samukallio/retro-z80/hardware/kicad/video.kicad_sch

## KiCad design hardware/kicad/video.kicad_sch (2024-03-21, an earlier design)

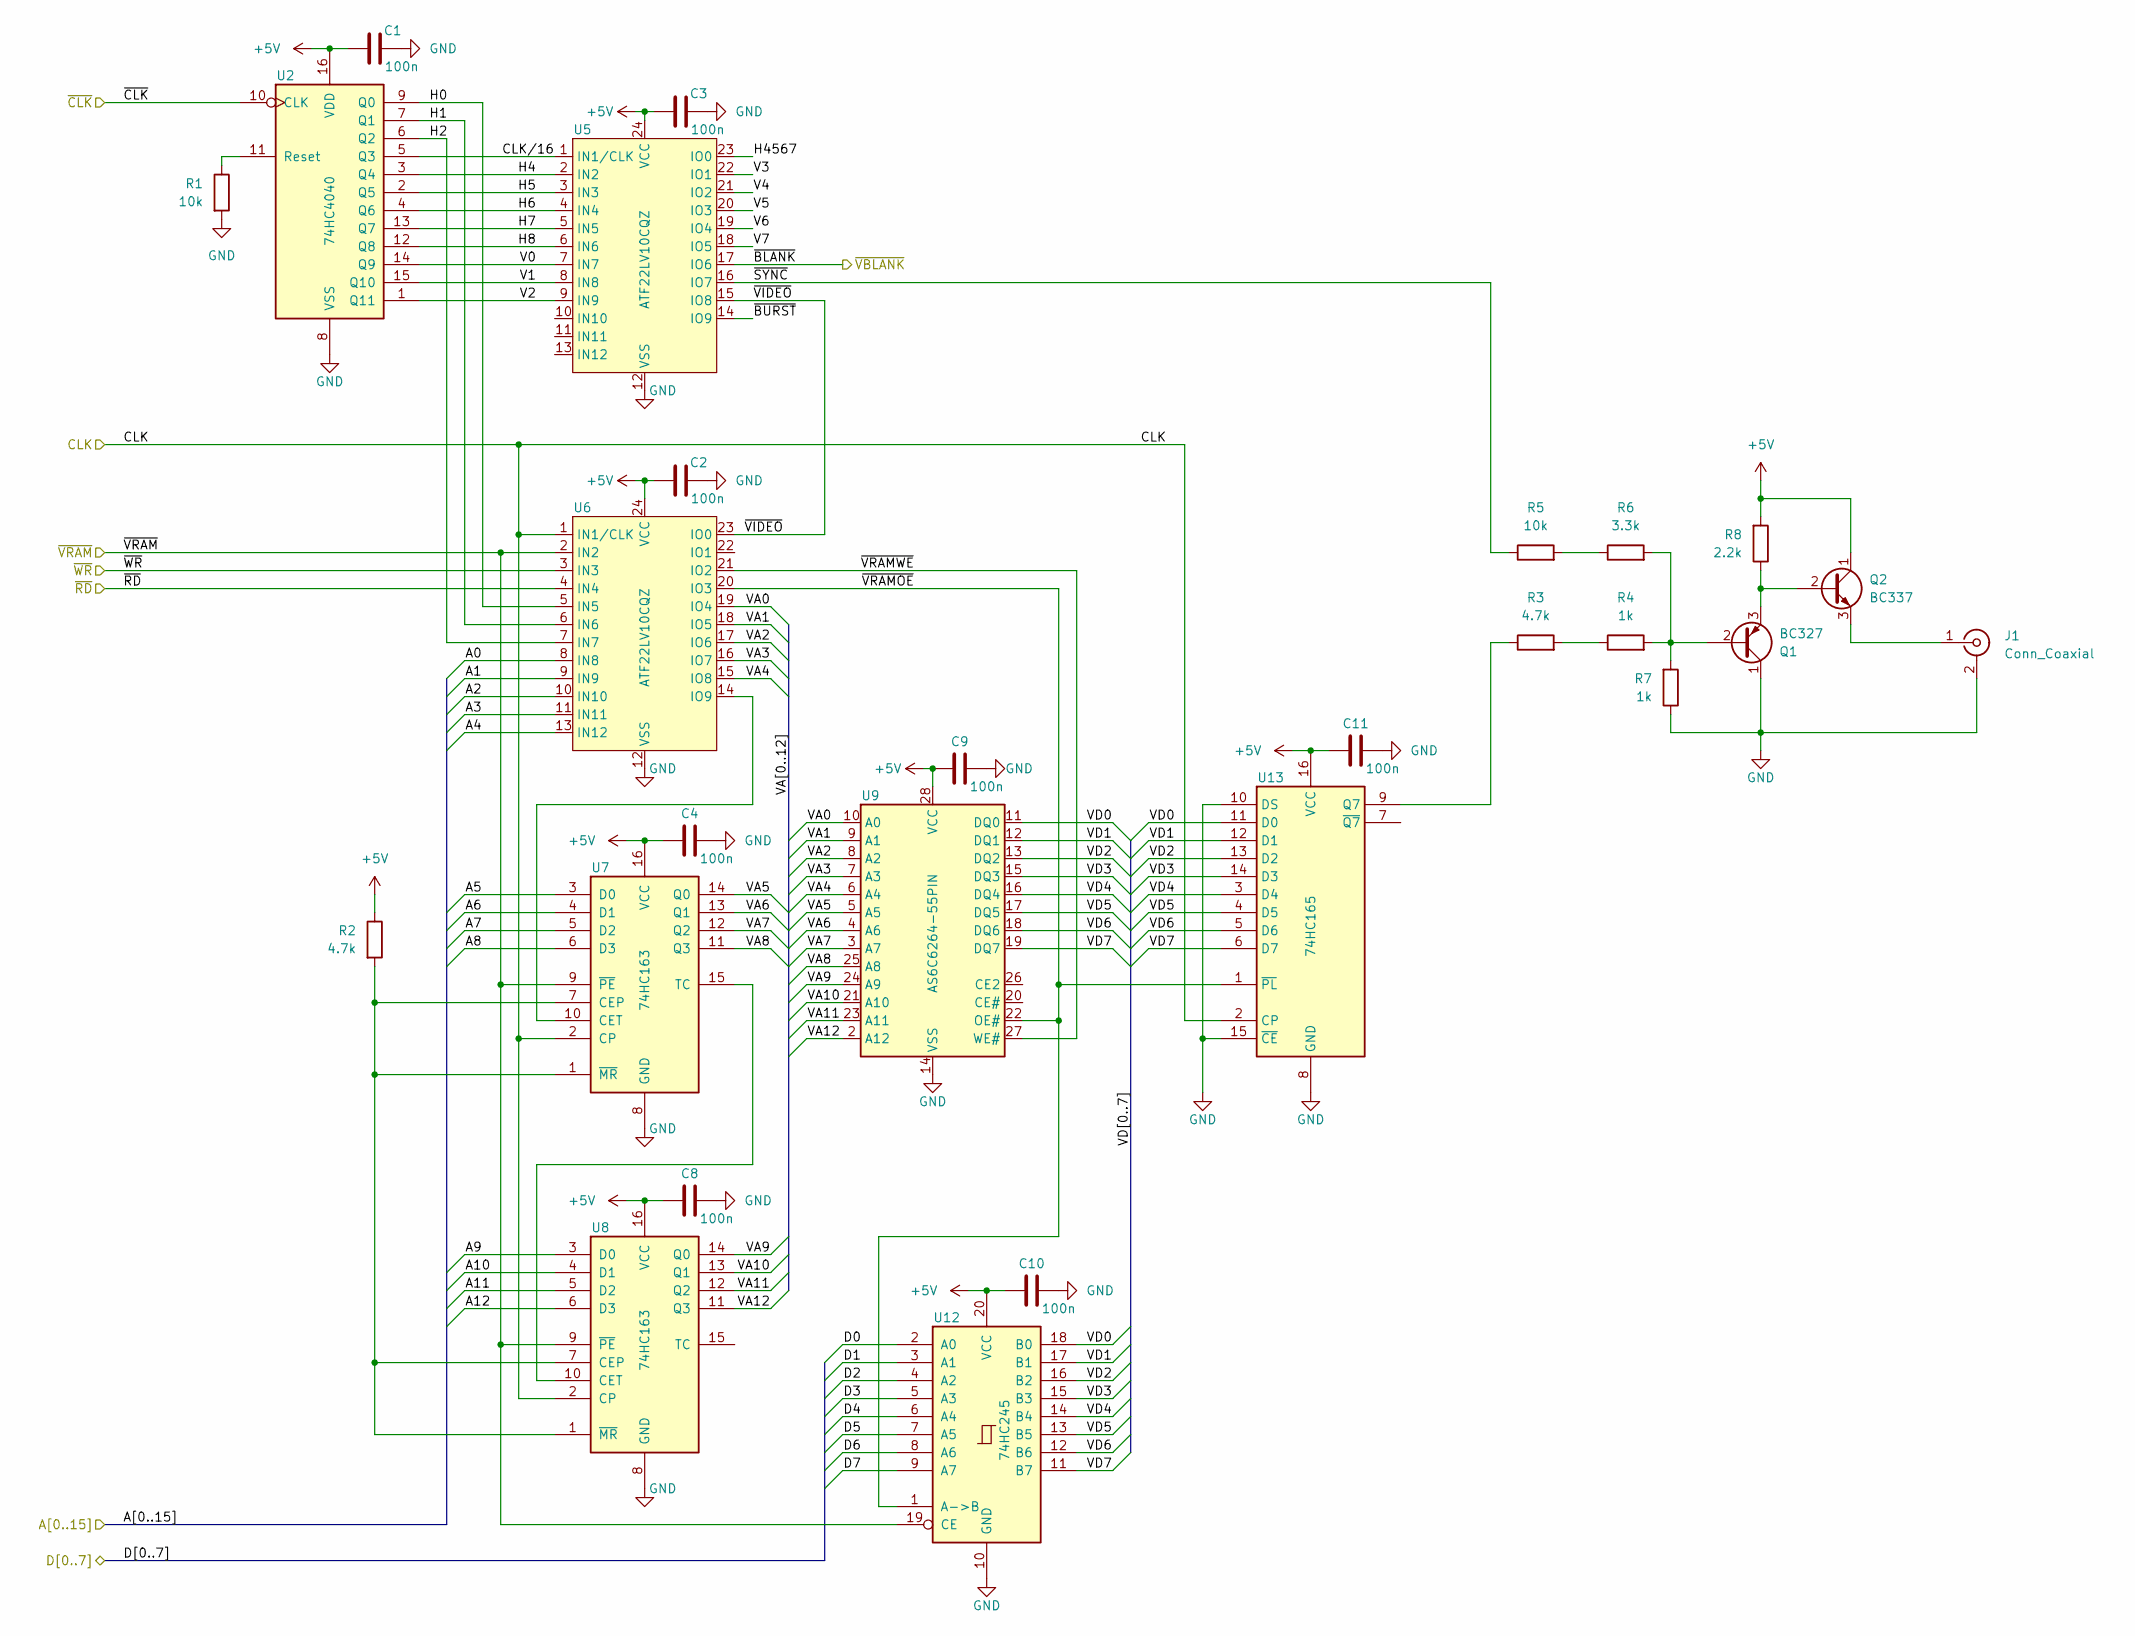
[picture p4: schematic video.kicad_sch]

Parts:
C1, C2, C3, C4, C8, C9, C10, C11: 100n
J1: Conn_Coaxial
Q1: BC327; TO-92_Inline
Q2: BC337; TO-92_Inline
R1, R5: 10k
R2, R3: 4.7k
R4, R7: 1k
R6: 3.3k
R8: 2.2k
U2: 74HC4040
U5, U6: ATF22LV10CQZ
U7, U8: 74HC163
U9: AS6C6264-55PIN; DIP-32_W15.24mm
U12: 74HC245
U13: 74HC165

Connections:
+5V: C1.1, C2.1, C3.1, C4.1, C8.1, C9.1, C10.1, C11.1, Q2.1 (C), R2.1, R8.2, U2.16 (VDD), U5.24 (VCC), U6.24 (VCC), U7.16 (VCC), U8.16 (VCC), U9.28 (VCC), U12.20 (VCC), U13.16 (VCC)
A0: U6.8 (IN8)
A1: U6.9 (IN9)
A2: U6.10 (IN10)
A3: U6.11 (IN11)
A4: U6.13 (IN12)
A5: U7.3 (D0)
A6: U7.4 (D1)
A7: U7.5 (D2)
A8: U7.6 (D3)
A9: U8.3 (D0)
A10: U8.4 (D1)
A11: U8.5 (D2)
A12: U8.6 (D3)
CLK: U6.1 (IN1/CLK), U7.2 (CP), U8.2 (CP), U13.2 (CP)
CLK/16: U2.5 (Q3), U5.1 (IN1/CLK)
D0: U12.2 (A0)
D1: U12.3 (A1)
D2: U12.4 (A2)
D3: U12.5 (A3)
D4: U12.6 (A4)
D5: U12.7 (A5)
D6: U12.8 (A6)
D7: U12.9 (A7)
GND: C1.2, C2.2, C3.2, C4.2, C8.2, C9.2, C10.2, C11.2, J1.2 (Ext), Q1.1 (C), R1.2, R7.1, U2.8 (VSS), U5.12 (VSS), U6.12 (VSS), U7.8 (GND), U8.8 (GND), U9.14 (VSS), U12.10 (GND), U13.8 (GND), U13.10 (DS), U13.15 (~CE)
H0: U2.9 (Q0), U6.5 (IN5)
H1: U2.7 (Q1), U6.6 (IN6)
H2: U2.6 (Q2), U6.7 (IN7)
H4: U2.3 (Q4), U5.2 (IN2)
H5: U2.2 (Q5), U5.3 (IN3)
H6: U2.4 (Q6), U5.4 (IN4)
H7: U2.13 (Q7), U5.5 (IN5)
H8: U2.12 (Q8), U5.6 (IN6)
H4567: U5.23 (IO0)
unnamed: J1.1 (In), Q2.3 (E)
unnamed: Q1.2 (B), R4.2, R6.2, R7.2
unnamed: Q1.3 (E), Q2.2 (B), R8.1
unnamed: R1.1, U2.11 (Reset)
unnamed: R2.2, U7.1 (~MR), U7.7 (CEP), U8.1 (~MR), U8.7 (CEP)
unnamed: R3.1, U13.9 (Q7)
unnamed: R3.2, R4.1
unnamed: R5.2, R6.1
unnamed: U6.14 (IO9), U7.10 (CET)
unnamed: U7.15 (TC), U8.10 (CET)
V0: U2.14 (Q9), U5.7 (IN7)
V1: U2.15 (Q10), U5.8 (IN8)
V2: U2.1 (Q11), U5.9 (IN9)
V3: U5.22 (IO1)
V4: U5.21 (IO2)
V5: U5.20 (IO3)
V6: U5.19 (IO4)
V7: U5.18 (IO5)
VA0: U6.19 (IO4), U9.10 (A0)
VA1: U6.18 (IO5), U9.9 (A1)
VA2: U6.17 (IO6), U9.8 (A2)
VA3: U6.16 (IO7), U9.7 (A3)
VA4: U6.15 (IO8), U9.6 (A4)
VA5: U7.14 (Q0), U9.5 (A5)
VA6: U7.13 (Q1), U9.4 (A6)
VA7: U7.12 (Q2), U9.3 (A7)
VA8: U7.11 (Q3), U9.25 (A8)
VA9: U8.14 (Q0), U9.24 (A9)
VA10: U8.13 (Q1), U9.21 (A10)
VA11: U8.12 (Q2), U9.23 (A11)
VA12: U8.11 (Q3), U9.2 (A12)
VD0: U9.11 (DQ0), U12.18 (B0), U13.11 (D0)
VD1: U9.12 (DQ1), U12.17 (B1), U13.12 (D1)
VD2: U9.13 (DQ2), U12.16 (B2), U13.13 (D2)
VD3: U9.15 (DQ3), U12.15 (B3), U13.14 (D3)
VD4: U9.16 (DQ4), U12.14 (B4), U13.3 (D4)
VD5: U9.17 (DQ5), U12.13 (B5), U13.4 (D5)
VD6: U9.18 (DQ6), U12.12 (B6), U13.5 (D6)
VD7: U9.19 (DQ7), U12.11 (B7), U13.6 (D7)
~BLANK: U5.17 (IO6)
~BURST: U5.14 (IO9)
~CLK: U2.10 (CLK)
~RD: U6.4 (IN4)
~SYNC: R5.1, U5.16 (IO7)
~VIDEO: U5.15 (IO8), U6.23 (IO0)
~VRAMOE: U6.20 (IO3), U9.22 (OE#), U12.1 (A->B), U13.1 (~PL)
~VRAMWE: U6.21 (IO2), U9.27 (WE#)
~VRAM: U6.2 (IN2), U7.9 (~PE), U8.9 (~PE), U12.19 (CE)
~WR: U6.3 (IN3)
