samukallio/retro-z80/hardware/kicad/z80.kicad_sch

## KiCad design hardware/kicad/z80.kicad_sch (2024-03-21, an earlier design)

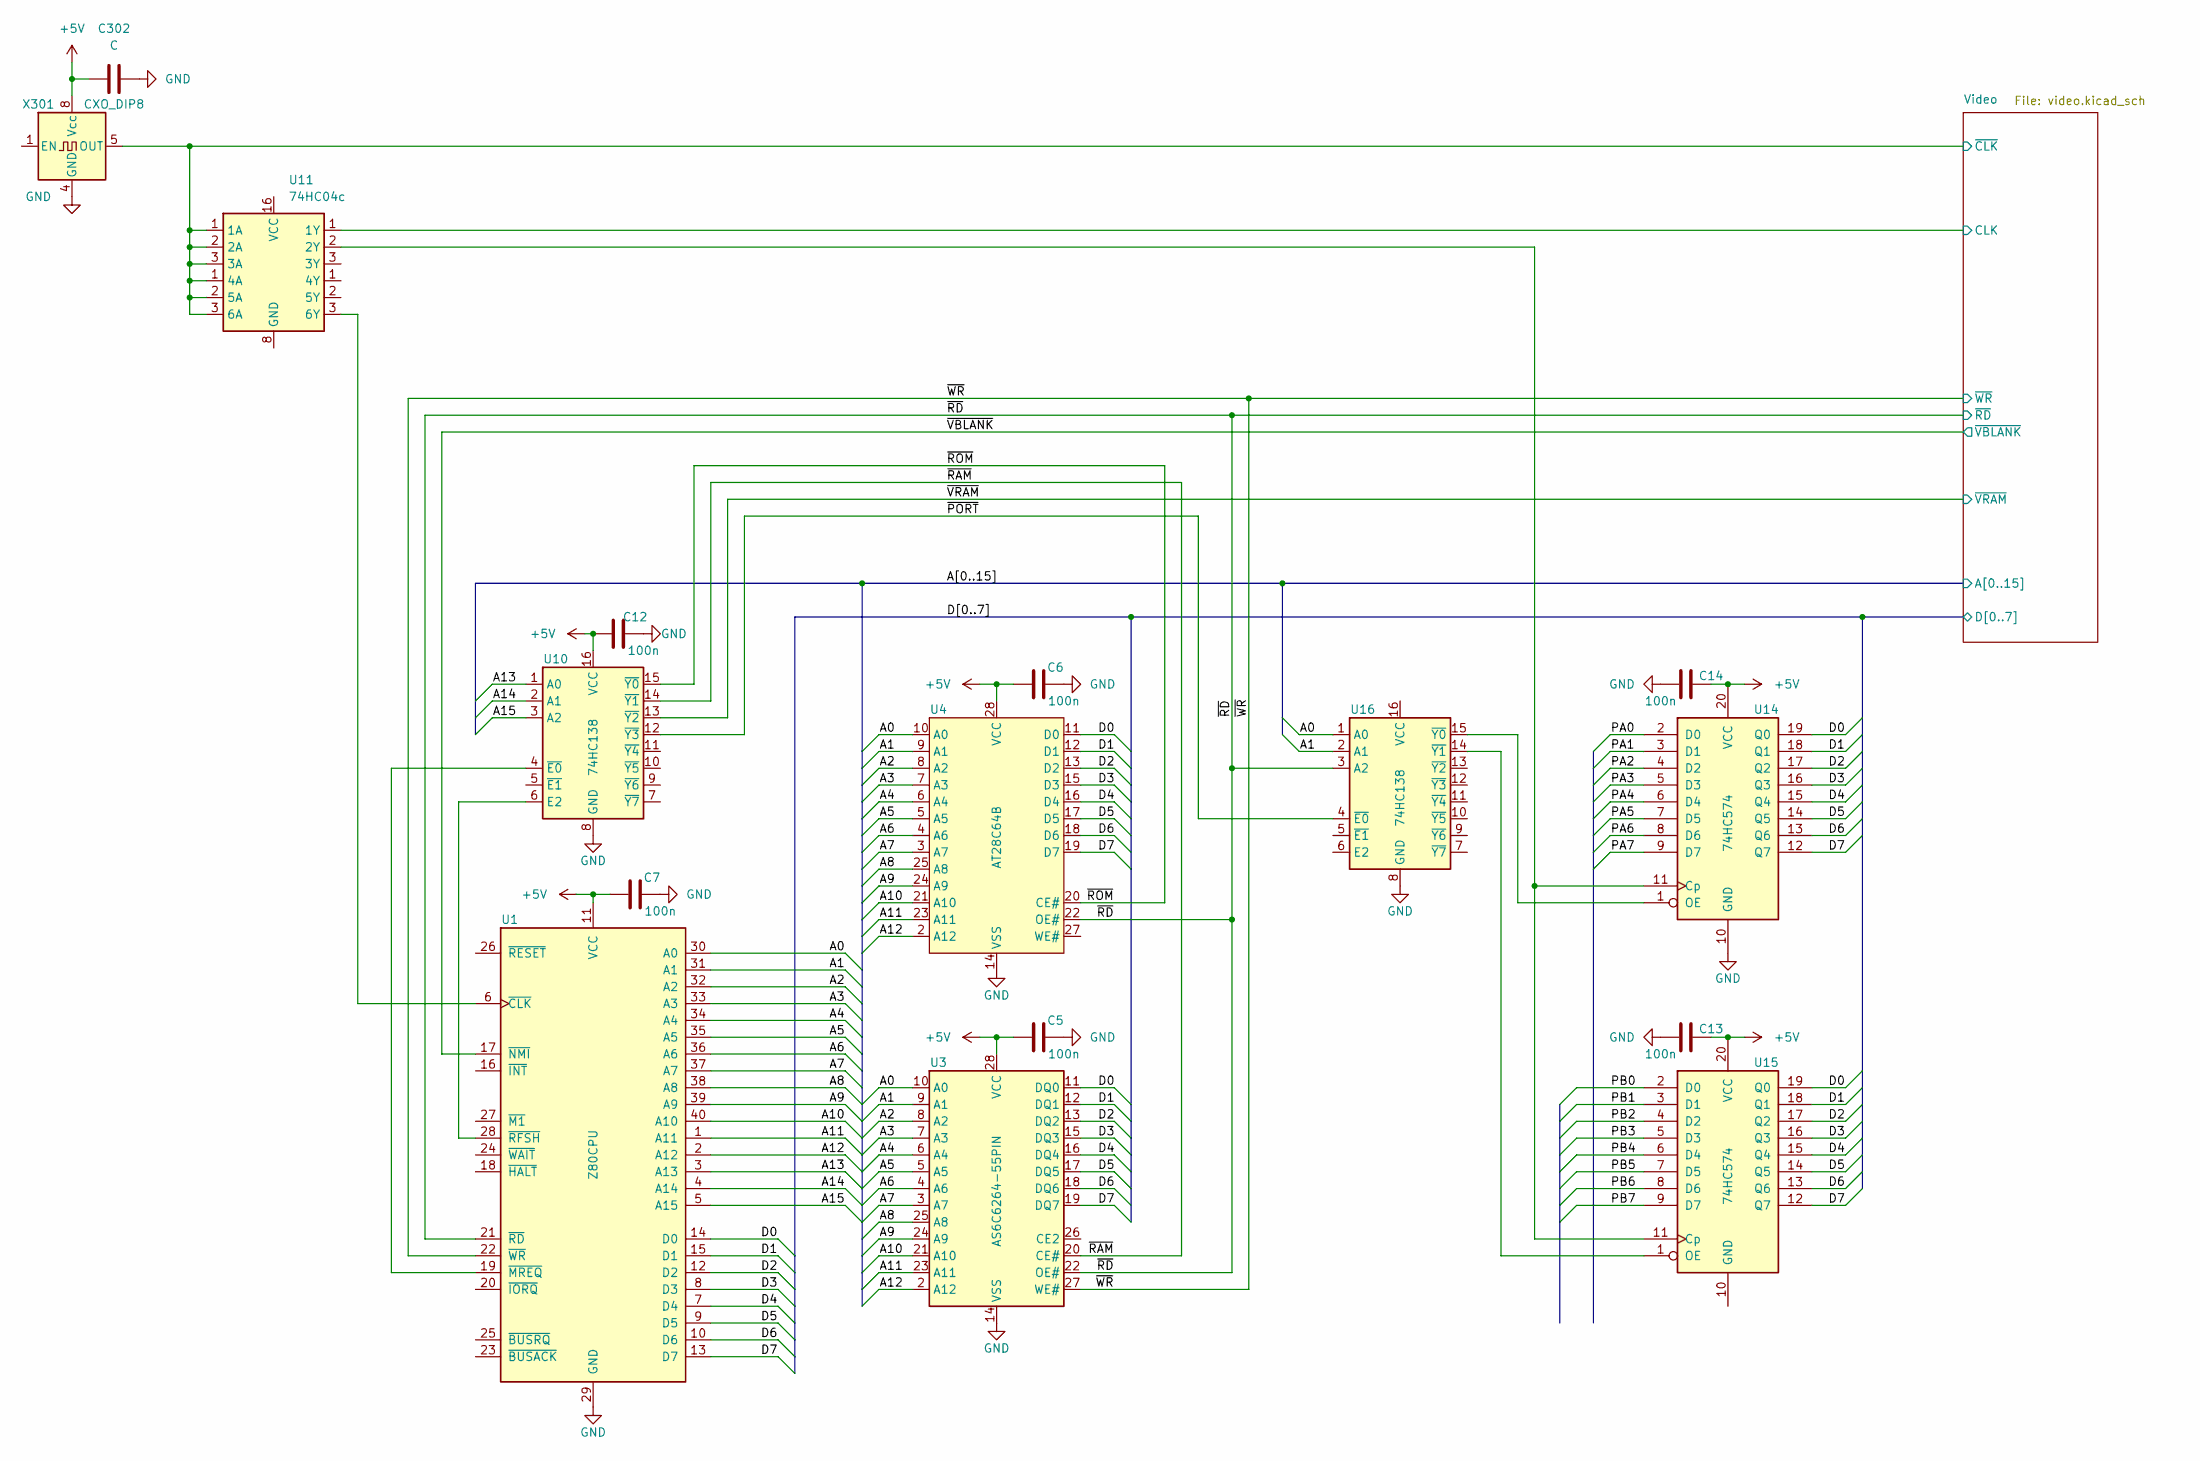
[picture p5: schematic z80.kicad_sch]

Parts:
C5, C6, C7, C12, C13, C14: 100n
C302: C
U1: Z80CPU
U3: AS6C6264-55PIN; DIP-32_W15.24mm
U4: AT28C64B
U10, U16: 74HC138
U11: 74HC04c
U14, U15: 74HC574
X301: CXO_DIP8; Oscillator_DIP-8

Connections:
+5V: C5.1, C6.1, C7.1, C12.1, C13.1, C14.1, C302.1, U1.11 (VCC), U3.28 (VCC), U4.28 (VCC), U10.16 (VCC), U14.20 (VCC), U15.20 (VCC), X301.8 (Vcc)
A0: U1.30 (A0), U3.10 (A0), U4.10 (A0), U16.1 (A0)
A1: U1.31 (A1), U3.9 (A1), U4.9 (A1), U16.2 (A1)
A2: U1.32 (A2), U3.8 (A2), U4.8 (A2)
A3: U1.33 (A3), U3.7 (A3), U4.7 (A3)
A4: U1.34 (A4), U3.6 (A4), U4.6 (A4)
A5: U1.35 (A5), U3.5 (A5), U4.5 (A5)
A6: U1.36 (A6), U3.4 (A6), U4.4 (A6)
A7: U1.37 (A7), U3.3 (A7), U4.3 (A7)
A8: U1.38 (A8), U3.25 (A8), U4.25 (A8)
A9: U1.39 (A9), U3.24 (A9), U4.24 (A9)
A10: U1.40 (A10), U3.21 (A10), U4.21 (A10)
A11: U1.1 (A11), U3.23 (A11), U4.23 (A11)
A12: U1.2 (A12), U3.2 (A12), U4.2 (A12)
A13: U1.3 (A13), U10.1 (A0)
A14: U1.4 (A14), U10.2 (A1)
A15: U1.5 (A15), U10.3 (A2)
CLK: U11.1 (1A)
D0: U1.14 (D0), U3.11 (DQ0), U4.11 (D0), U14.19 (Q0), U15.19 (Q0)
D1: U1.15 (D1), U3.12 (DQ1), U4.12 (D1), U14.18 (Q1), U15.18 (Q1)
D2: U1.12 (D2), U3.13 (DQ2), U4.13 (D2), U14.17 (Q2), U15.17 (Q2)
D3: U1.8 (D3), U3.15 (DQ3), U4.15 (D3), U14.16 (Q3), U15.16 (Q3)
D4: U1.7 (D4), U3.16 (DQ4), U4.16 (D4), U14.15 (Q4), U15.15 (Q4)
D5: U1.9 (D5), U3.17 (DQ5), U4.17 (D5), U14.14 (Q5), U15.14 (Q5)
D6: U1.10 (D6), U3.18 (DQ6), U4.18 (D6), U14.13 (Q6), U15.13 (Q6)
D7: U1.13 (D7), U3.19 (DQ7), U4.19 (D7), U14.12 (Q7), U15.12 (Q7)
GND: C5.2, C6.2, C7.2, C12.2, C13.2, C14.2, C302.2, U1.29 (GND), U3.14 (VSS), U4.14 (VSS), U10.8 (GND), U14.10 (GND), U16.8 (GND), X301.4 (GND)
unnamed: U1.6 (~CLK), U11.3 (3A)
unnamed: U1.19 (~MREQ), U10.4 (~E0)
unnamed: U1.28 (~RFSH), U10.6 (E2)
unnamed: U11.2 (2A), U14.11 (Cp), U15.11 (Cp)
unnamed: U14.1 (OE), U16.15 (~Y0)
unnamed: U15.1 (OE), U16.14 (~Y1)
PA0: U14.2 (D0)
PA1: U14.3 (D1)
PA2: U14.4 (D2)
PA3: U14.5 (D3)
PA4: U14.6 (D4)
PA5: U14.7 (D5)
PA6: U14.8 (D6)
PA7: U14.9 (D7)
PB0: U15.2 (D0)
PB1: U15.3 (D1)
PB2: U15.4 (D2)
PB3: U15.5 (D3)
PB4: U15.6 (D4)
PB5: U15.7 (D5)
PB6: U15.8 (D6)
PB7: U15.9 (D7)
~CLK: U11.1 (1A), U11.2 (2A), U11.3 (3A), X301.5 (OUT)
~PORT: U10.12 (~Y3), U16.4 (~E0)
~RAM: U3.20 (CE#), U10.14 (~Y1)
~RD: U1.21 (~RD), U3.22 (OE#), U4.22 (OE#), U16.3 (A2)
~ROM: U4.20 (CE#), U10.15 (~Y0)
~VBLANK: U1.17 (~NMI)
~VRAM: U10.13 (~Y2)
~WR: U1.22 (~WR), U3.27 (WE#)
